Skipper7718/NullBot/software/ESPHelper/components/ultrasonic/ultrasonic.c

#include "ultrasonic.h"
#include <freertos/FreeRTOS.h>
#include <freertos/task.h>
#include <sys/time.h>
#include "rom/ets_sys.h"

#define TRIGGER_LOW_DELAY 4
#define TRIGGER_HIGH_DELAY 10
#define PING_TIMEOUT 6000
#define ROUNDTRIP 58

static portMUX_TYPE mux = portMUX_INITIALIZER_UNLOCKED;

static inline uint32_t get_time_us()
{
    struct timeval tv;
    gettimeofday(&tv, NULL);
    return tv.tv_usec;
}

#define timeout_expired(start, len) ((uint32_t)(get_time_us() - (start)) >= (len))

#define RETURN_CRTCAL(MUX, RES) do { portEXIT_CRITICAL(&MUX); return RES; } while(0)

void ultrasonic_init(const ultrasonic_sensor_t *dev)
{
    gpio_pad_select_gpio( dev->trigger_pin );
    gpio_pad_select_gpio( dev->echo_pin );
    gpio_set_direction(dev->trigger_pin, GPIO_MODE_OUTPUT);
    gpio_set_direction(dev->echo_pin, GPIO_MODE_INPUT);

    gpio_set_level(dev->trigger_pin, 0);
}

esp_err_t ultrasonic_measure_cm(const ultrasonic_sensor_t *dev, uint32_t max_distance, uint32_t *distance)
{
    if (!distance)
        return ESP_ERR_INVALID_ARG;

    portENTER_CRITICAL(&mux);

    // Low2..4, high 10
    gpio_set_level(dev->trigger_pin, 0);
    ets_delay_us(TRIGGER_LOW_DELAY);
    gpio_set_level(dev->trigger_pin, 1);
    ets_delay_us(TRIGGER_HIGH_DELAY);
    gpio_set_level(dev->trigger_pin, 0);

    if (gpio_get_level(dev->echo_pin))
        RETURN_CRTCAL(mux, ESP_ERR_ULTRASONIC_PING);

    // wait for echo
    uint32_t start = get_time_us();
    while (!gpio_get_level(dev->echo_pin))
    {
        if (timeout_expired(start, PING_TIMEOUT))
            RETURN_CRTCAL(mux, ESP_ERR_ULTRASONIC_PING_TIMEOUT);
    }

    // lets goo measure :)
    uint32_t echo_start = get_time_us();
    uint32_t time = echo_start;
    uint32_t meas_timeout = echo_start + max_distance * ROUNDTRIP;
    while (gpio_get_level(dev->echo_pin))
    {
        time = get_time_us();
        if (timeout_expired(echo_start, meas_timeout))
            RETURN_CRTCAL(mux, ESP_ERR_ULTRASONIC_ECHO_TIMEOUT);
    }
    portEXIT_CRITICAL(&mux);

    *distance = (time - echo_start) / ROUNDTRIP;

    return ESP_OK;
}
